basson/qym-filamet-dryer/cad/dry.stp

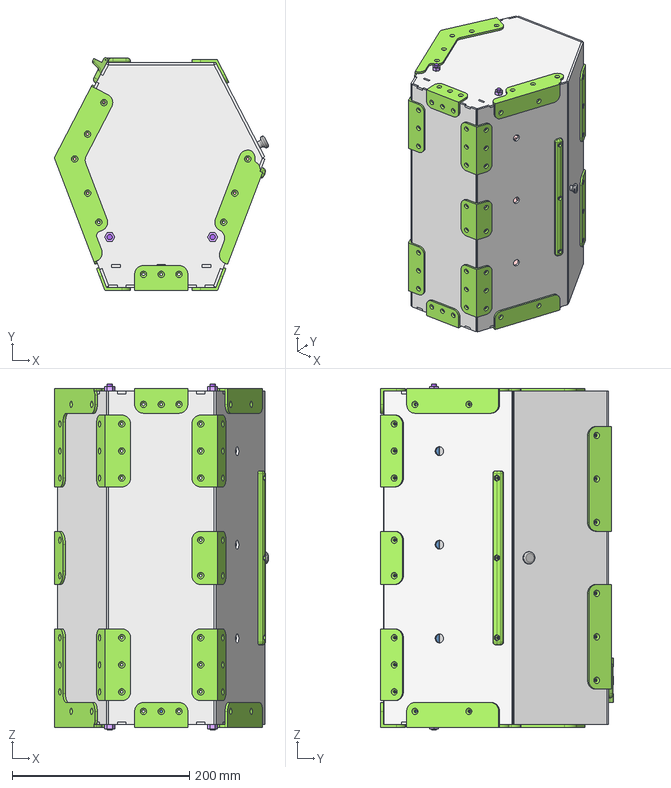
[picture p18: CAD file, 2024-01-19]
cad/dry.stp
241.7 x 262.2 x 390.0 mm
