basson/qym-filamet-dryer/cad/Streang_Beam_Bottom.stp

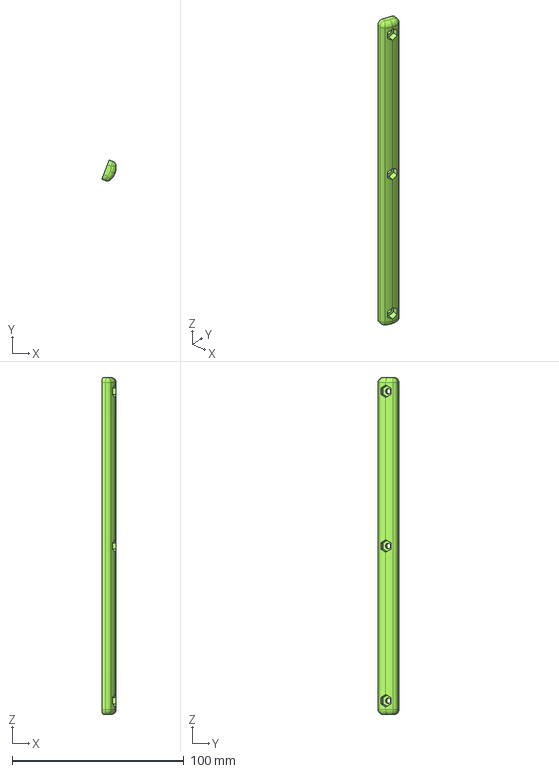
[picture p19: CAD file, 2024-01-19]
cad/Streang_Beam_Bottom.stp
8.39 x 12.2 x 196.0 mm
