basson/qym-filamet-dryer/cad/Hinge_cover.stp

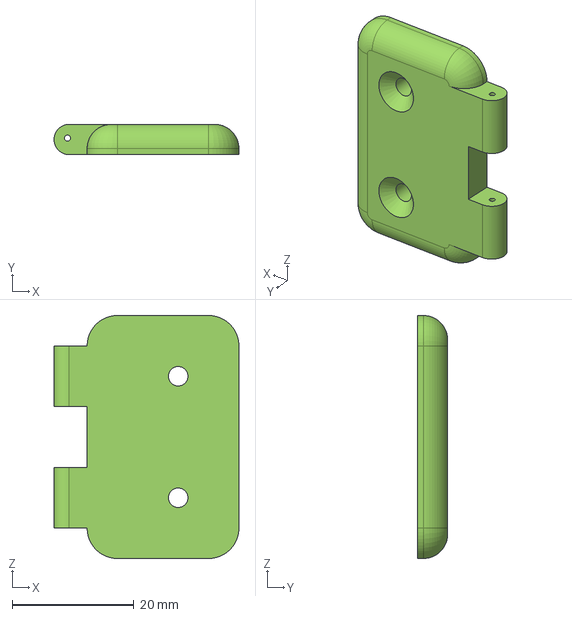
[picture p20: CAD file, 2024-01-19]
cad/Hinge_cover.stp
30.4 x 5.00 x 40.0 mm
