basson/qym-filamet-dryer/cad/Corner_back_centered.stp

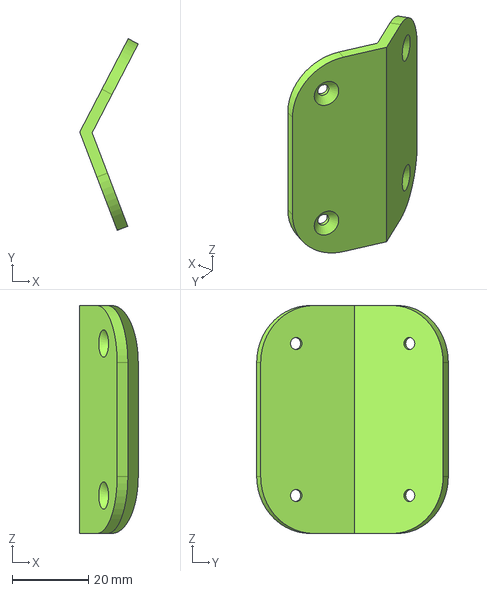
[picture p21: CAD file, 2024-01-19]
cad/Corner_back_centered.stp
15.4 x 50.5 x 60.0 mm
