basson/qym-filamet-dryer/cad/Corner_bottom_side.stp

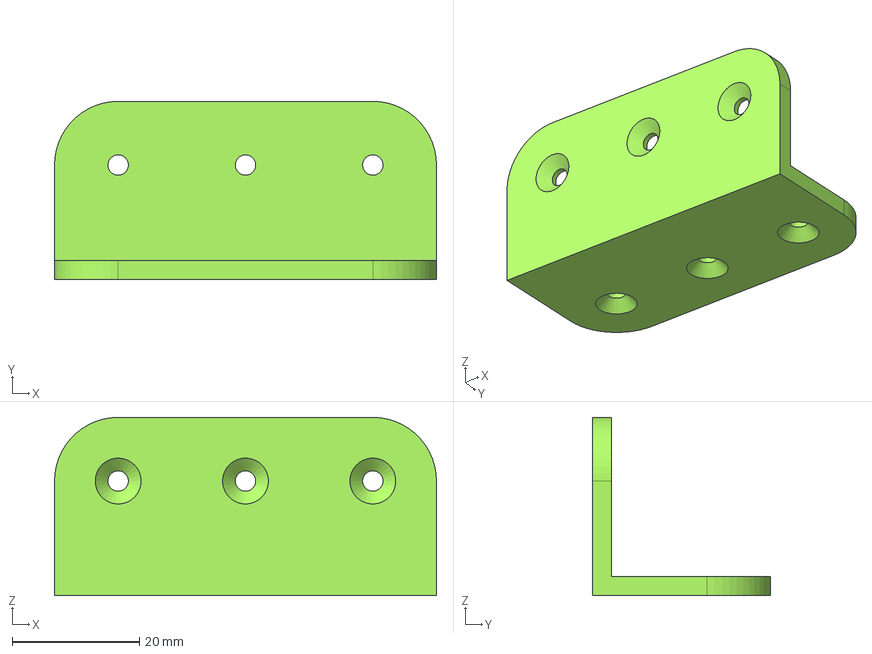
[picture p22: CAD file, 2024-01-19]
cad/Corner_bottom_side.stp
60.0 x 28.0 x 28.0 mm
